jnthas/pinch/App/components/w25qxx.h

#ifndef __W25QXX_H__
#define __W25QXX_H__

#include <stdint.h>
#include <stdbool.h>
#include "ch552.h"
#include "debug.h"
#include "spi.h"
#include "../core/Print.h"


#define SPIFLASH_WRITEENABLE      0x06        // write enable
#define SPIFLASH_WRITEDISABLE     0x04        // write disable

#define SPIFLASH_BLOCKERASE_4K    0x20        // erase one 4K block of flash memory
#define SPIFLASH_BLOCKERASE_32K   0x52        // erase one 32K block of flash memory
#define SPIFLASH_BLOCKERASE_64K   0xD8        // erase one 64K block of flash memory
#define SPIFLASH_CHIPERASE        0x60        // chip erase (may take several seconds depending on size)
                                              // but no actual need to wait for completion (instead need to check the status register BUSY bit)
#define SPIFLASH_STATUSREAD       0x05        // read status register
#define SPIFLASH_STATUSWRITE      0x01        // write status register
#define SPIFLASH_ARRAYREAD        0x0B        // read array (fast, need to add 1 dummy byte after 3 address bytes)
#define SPIFLASH_ARRAYREADLOWFREQ 0x03        // read array (low frequency)

#define SPIFLASH_SLEEP            0xB9        // deep power down
#define SPIFLASH_WAKE             0xAB        // deep power wake up
#define SPIFLASH_BYTEPAGEPROGRAM  0x02        // write (1 to 256bytes)
#define SPIFLASH_IDREAD           0x9F        // read JEDEC manufacturer and device ID (2 bytes, specific bytes for each manufacturer and device)
                                              // Example for Atmel-Adesto 4Mbit AT25DF041A: 0x1F44 (page 27: http://www.adestotech.com/sites/default/files/datasheets/doc3668.pdf)
                                              // Example for Winbond 4Mbit W25X40CL: 0xEF30 (page 14: http://www.winbond.com/NR/rdonlyres/6E25084C-0BFE-4B25-903D-AE10221A0929/0/W25X40CL.pdf)
#define SPIFLASH_MACREAD          0x4B        // read unique ID number (MAC)

#define FLASH_BUFFER_SIZE 32


extern __xdata uint8_t UNIQUEID[8];
extern __xdata uint8_t _sbuffer[FLASH_BUFFER_SIZE];


/* Hardware interface definition */
/******************************************************************************
Use CH554 hardware SPI interface
         CH554        DIR       
         P1.4        <==>       SCS
         P1.5        <==>       MOSI
         P1.6        <==>       MISO
         P1.7        <==>       SCK
*******************************************************************************/

uint8_t readByte(__xdata uint32_t addr);
__xdata uint16_t readDeviceId(void);
void  SPISetup(void);
uint8_t* readUniqueId();
void readBytes(__xdata uint32_t addr, void* buf, __xdata uint16_t len);
bool busy();
uint8_t readStatus();
void enableWrite();
void writeByte(__xdata uint32_t addr, uint8_t byt);
void writeBytes(__xdata uint32_t addr, const void* buf, __xdata uint16_t len);
void chipErase();
void blockErase4K(__xdata uint32_t addr);
void sleep();
void wakeup();


#endif
